goopypanther/OpenFieldProbe/0006_h_field_probe_15mm.sch

## EAGLE design 0006_h_field_probe_15mm.sch (2021-02-04)

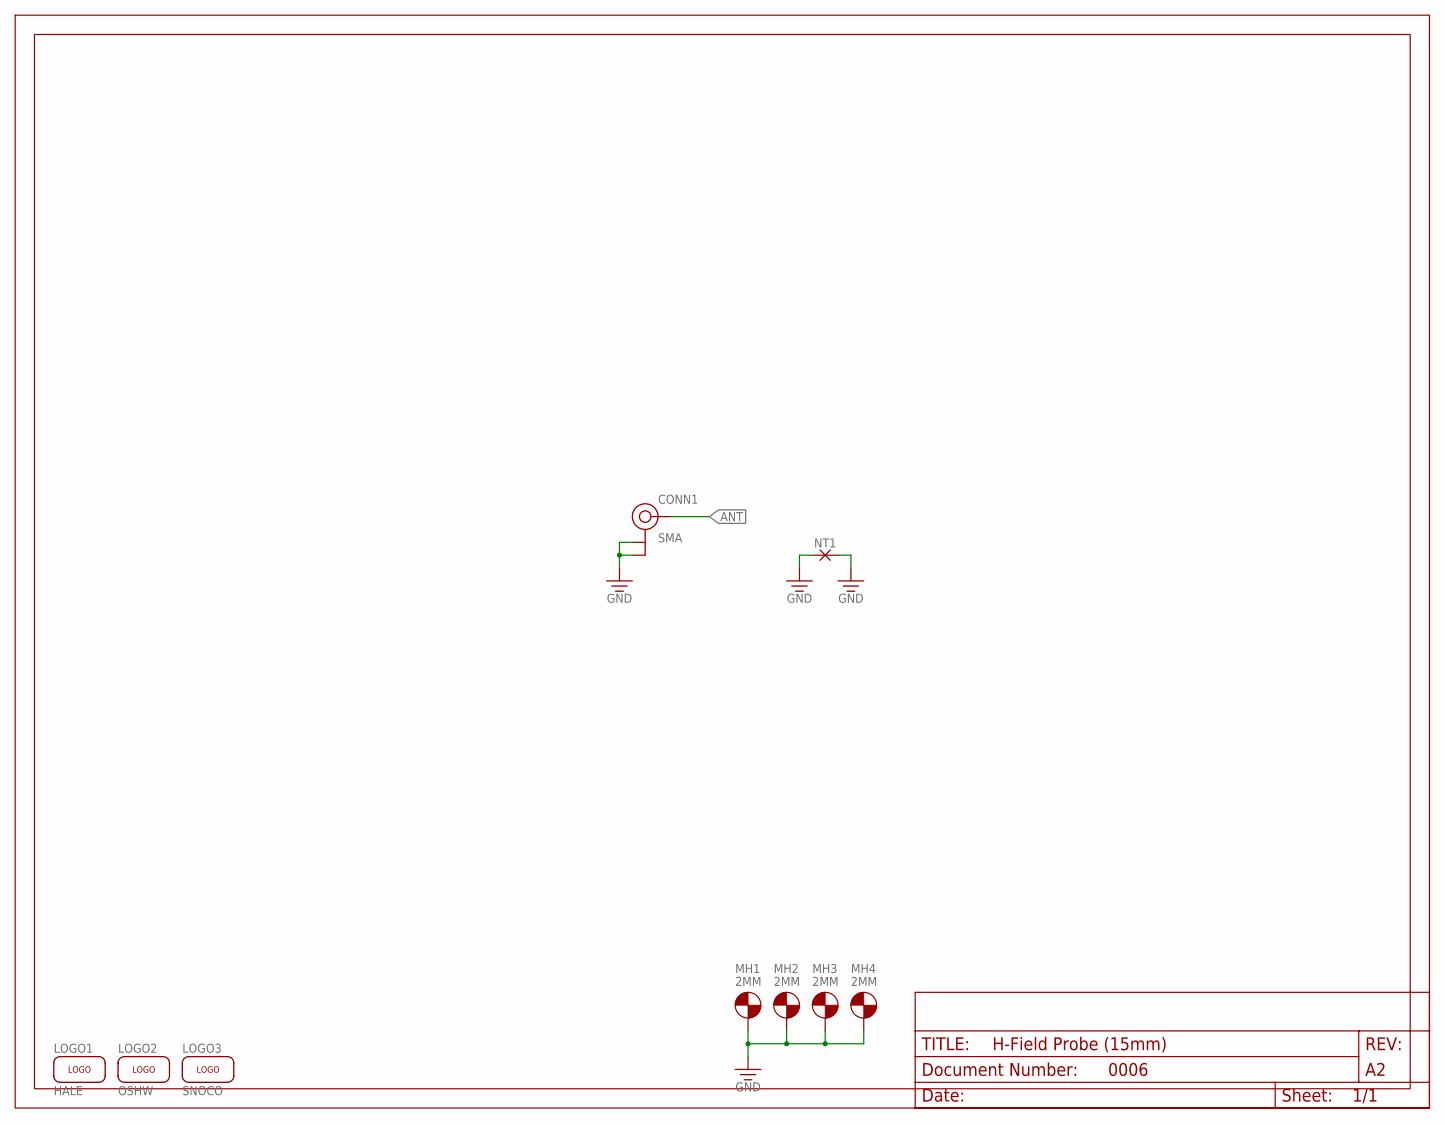
[picture p7: schematic 0006_h_field_probe_15mm.sch]

Parts:
CONN1: SMA; SMA-EDGE-6.5MM
LOGO1: HALE; HALE-SILK-ICON
LOGO2: OSHW; OSHW-SILK-ICON
LOGO3: SNOCO; SNOCO-SILK-ICON
MH1, MH2, MH3, MH4: 2MM; MH-M2-ELEC
NT1: NETTIE-VIA-TB
U$2: FRAME-8.5X11-LANDSCAPE-LET; FRAME-8.5X11-LANDSCAPE

Connections:
ANT: CONN1.2 (SIGNAL)
GND: CONN1.1 (GND), CONN1.4 (GND), MH1.1, MH2.1, MH3.1, MH4.1, NT1.1, NT1.2
