goopypanther/OpenFieldProbe/0007_h_field_probe_5mm.sch

## EAGLE design 0007_h_field_probe_5mm.sch (2021-02-03)

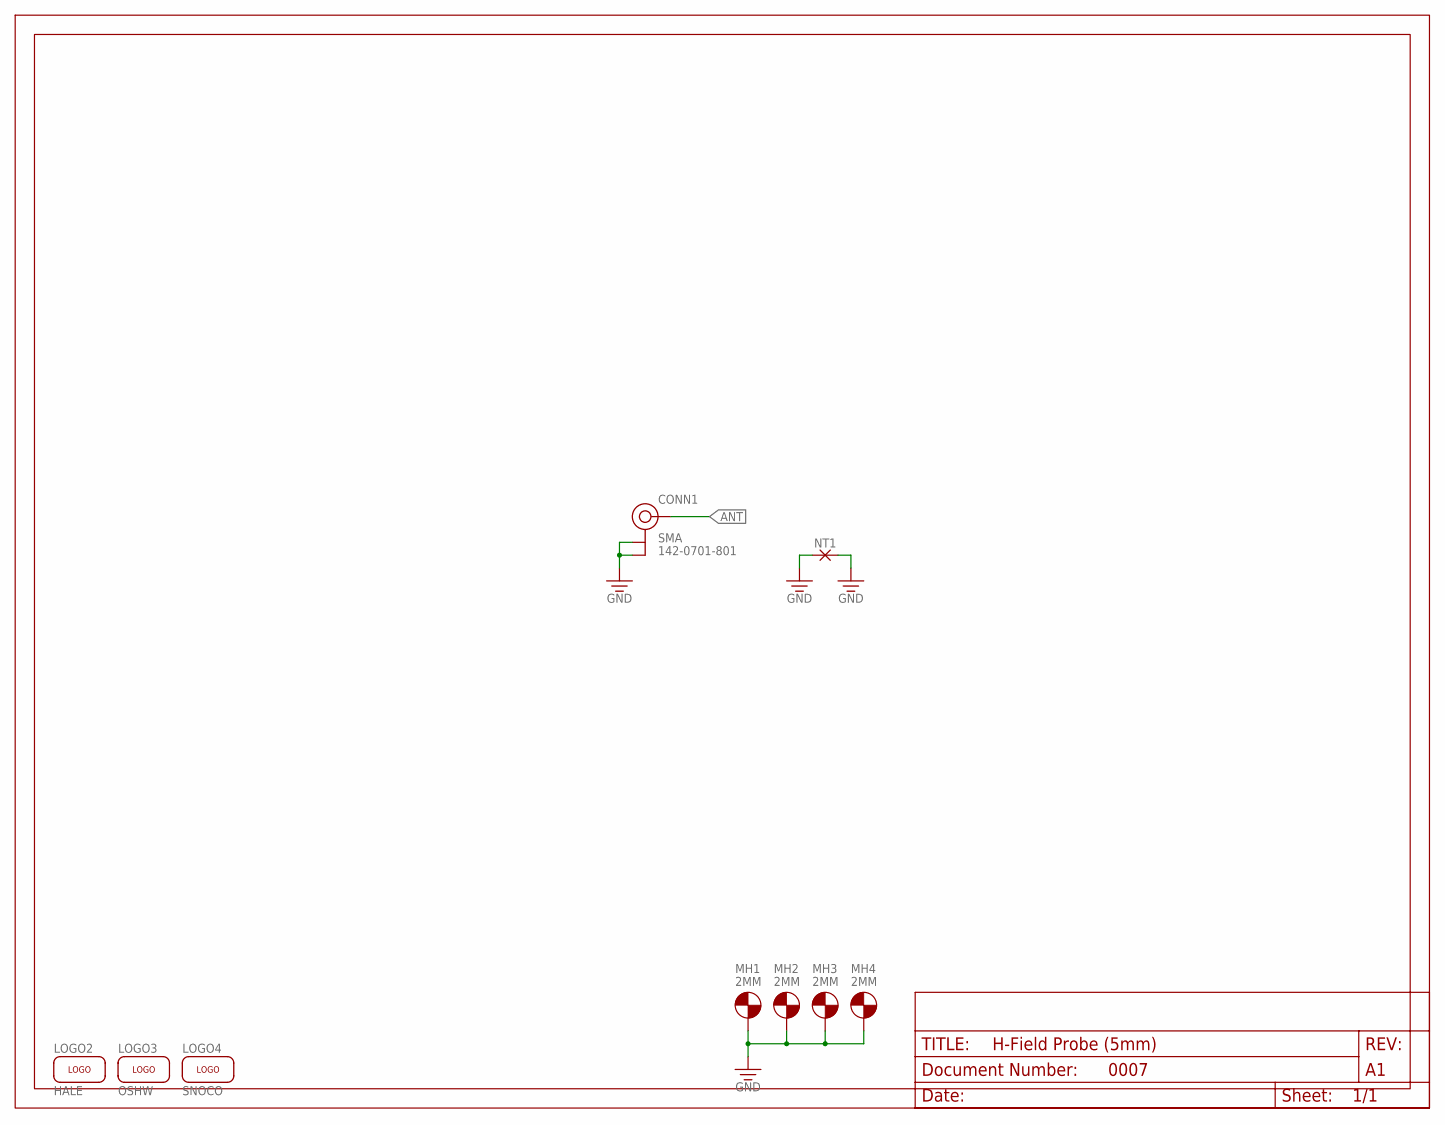
[picture p8: schematic 0007_h_field_probe_5mm.sch]

Parts:
CONN1: SMA; SMA-142-0701-801
LOGO2: HALE; HALE-SILK-ICON
LOGO3: OSHW; OSHW-SILK-ICON
LOGO4: SNOCO; SNOCO-SILK-ICON
MH1, MH2, MH3, MH4: 2MM; MH-M2-ELEC
NT1: NETTIE-VIA-TB
U$2: FRAME-8.5X11-LANDSCAPE-LET; FRAME-8.5X11-LANDSCAPE

Connections:
ANT: CONN1.2 (SIGNAL)
GND: CONN1.1 (GND), CONN1.4 (GND), MH1.1, MH2.1, MH3.1, MH4.1, NT1.1, NT1.2
